OneAudio/WBLNA/3D/WLNA_3Dview1.jpg

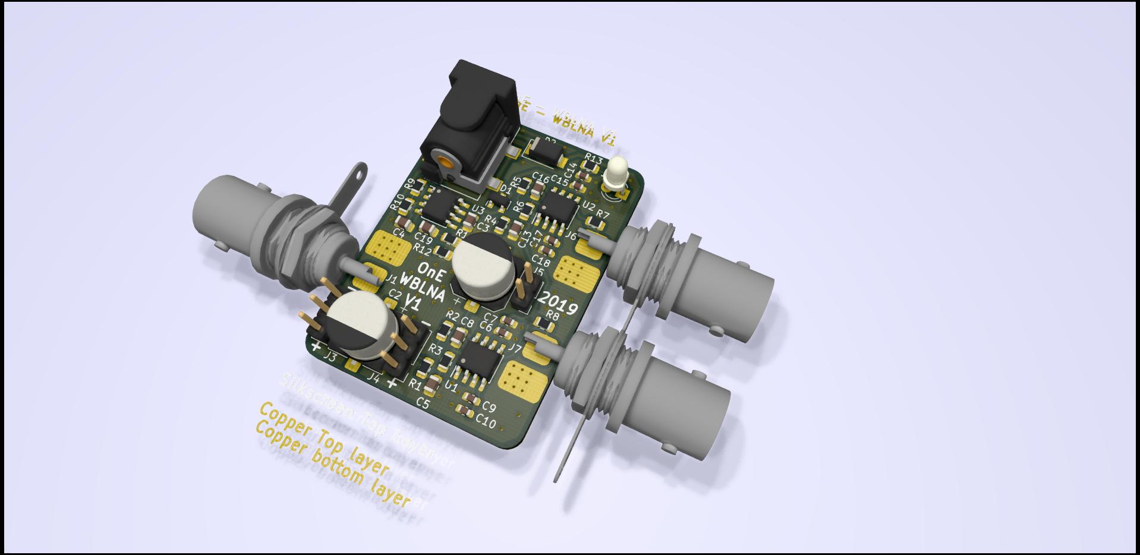
3D/WLNA_3Dview1.jpg
