OneAudio/WBLNA/3D/WLNA_3Dview2.jpg

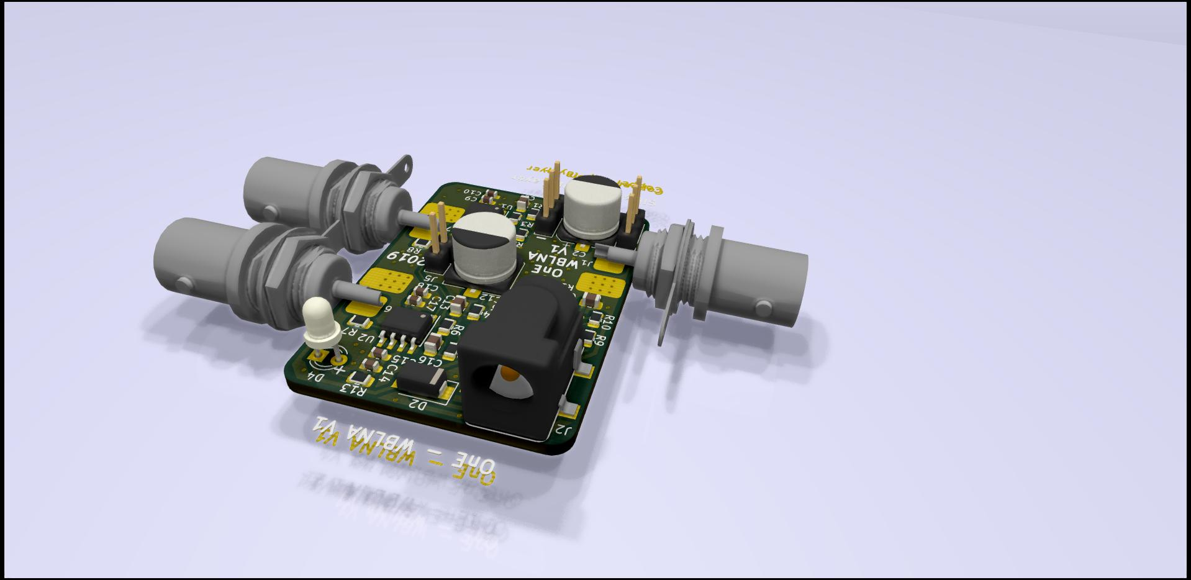
3D/WLNA_3Dview2.jpg
