OneAudio/WBLNA/3D/WLNA_3Dview3.jpg

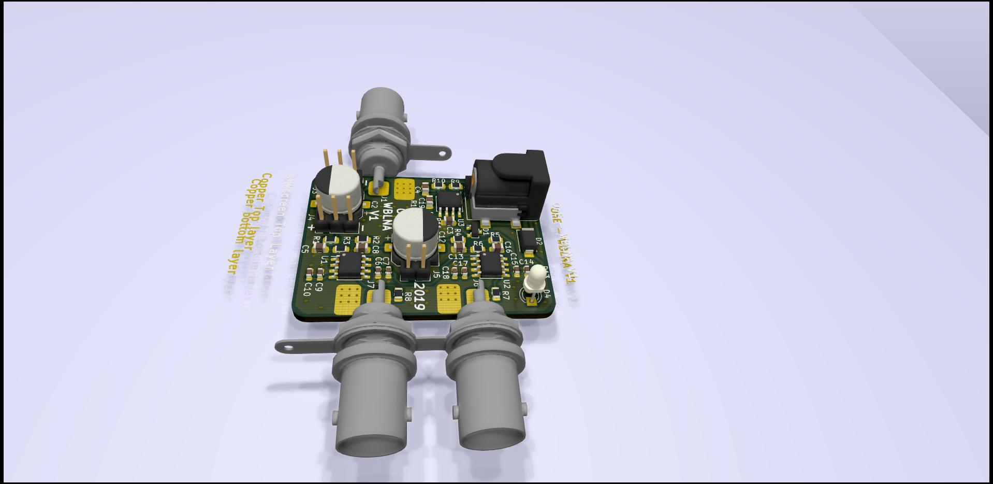
3D/WLNA_3Dview3.jpg
