OneAudio/WBLNA/Pictures/WBLNA_06.jpg

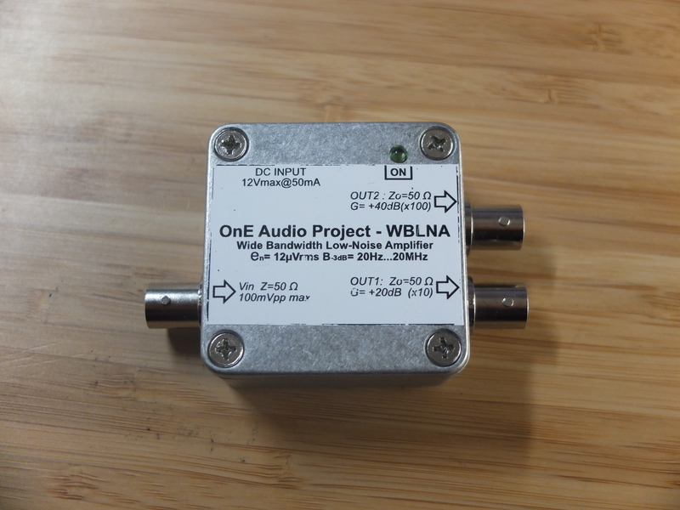
Pictures/WBLNA_06.jpg
