OneAudio/WBLNA/Pictures/WBLNA_08.jpg

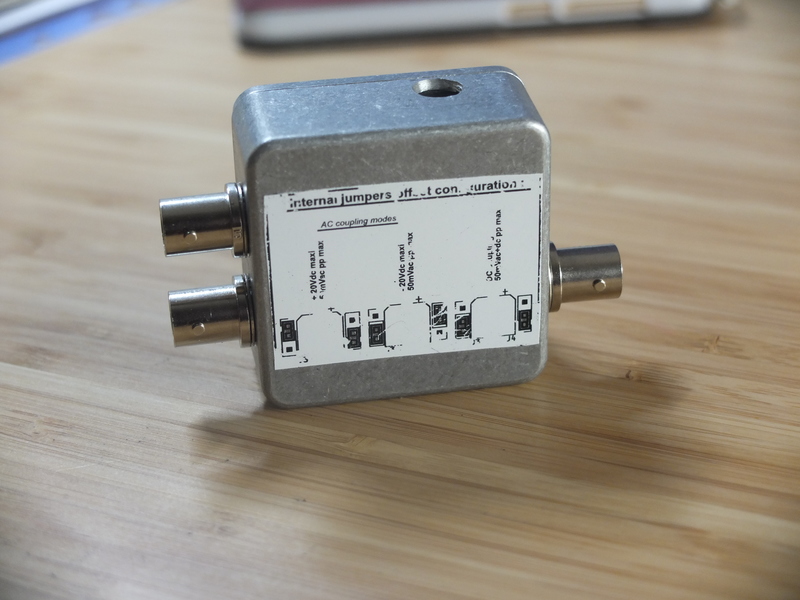
Pictures/WBLNA_08.jpg
