OneAudio/WBLNA/Pictures/WBLNA_09.jpg

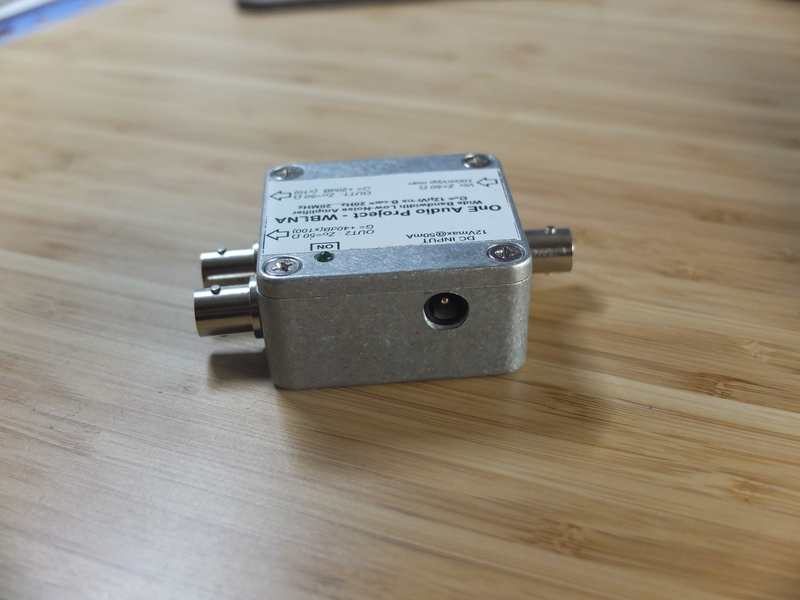
Pictures/WBLNA_09.jpg
