OneAudio/WBLNA/Simulations/WBLNA_noise-denstity.jpg

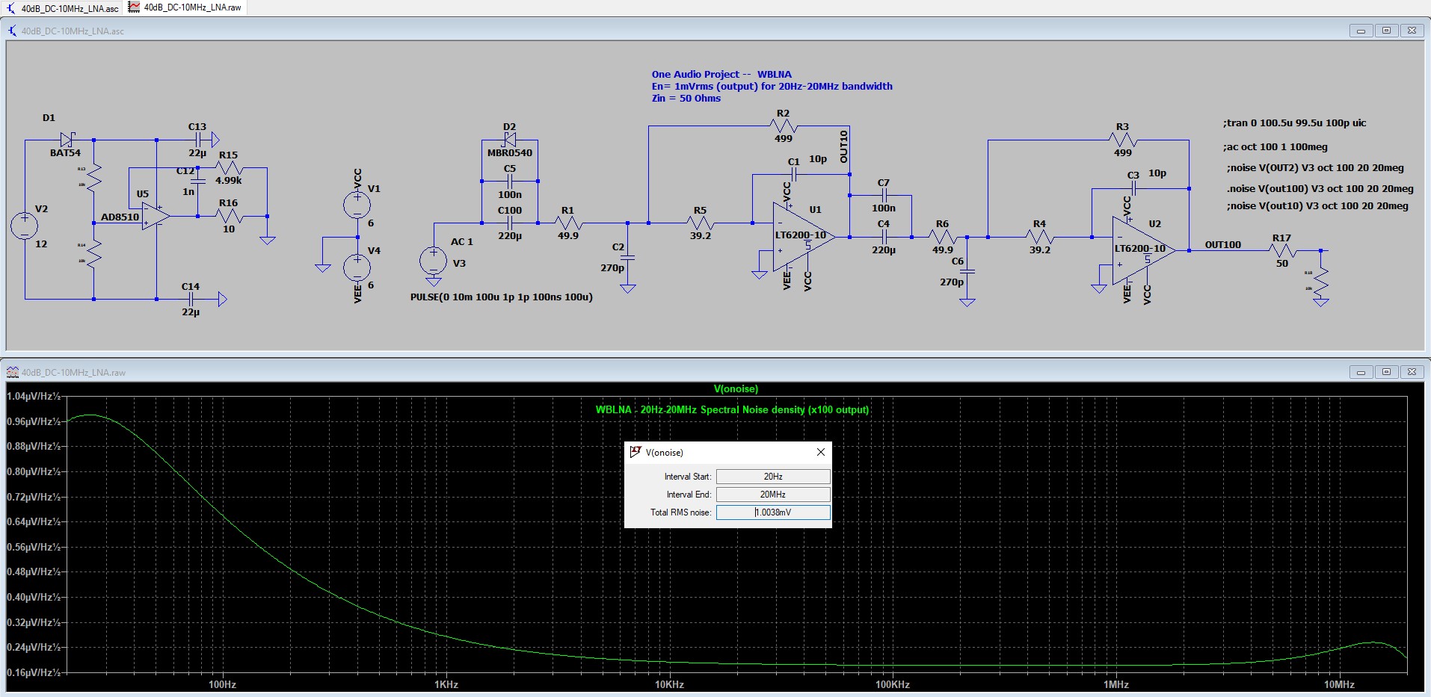
Simulations/WBLNA_noise-denstity.jpg
